Vitor-Marini/S.B.R/media/IMG_4792.JPEG

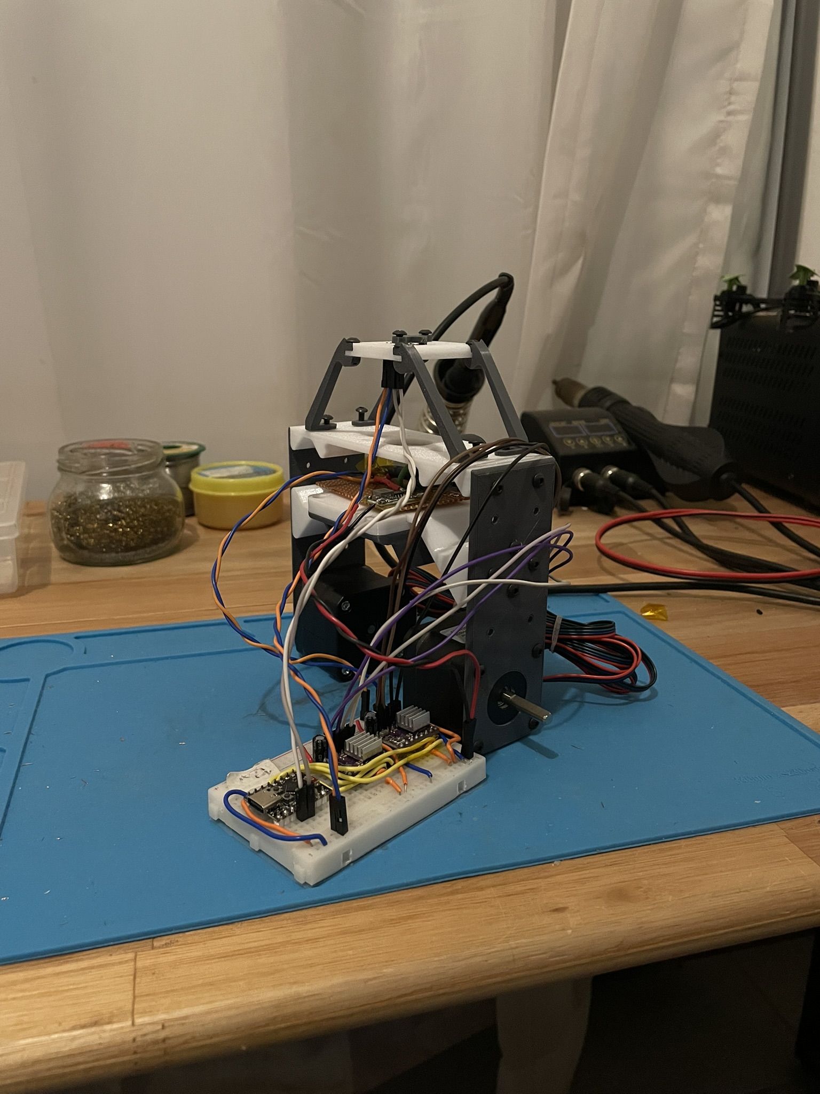
media/IMG_4792.JPEG
