Vitor-Marini/S.B.R/firmware/robot/S.B.R mk2/include/cli.hpp

#ifndef CLI_HPP
#define CLI_HPP

#include <Arduino.h>

class CLI {
public:
    void begin();
    void update();

private:
    String _buffer;
    void _processLine(const String& line);
    void _printPrompt();
    void _printHelp();
};

extern CLI cli;
#endif
